mattncsu/ESPixelClock/examples/ESPixelClock/patterns.h

/*
   ESP32 FastLED WebServer: https://github.com/jasoncoon/esp32-fastled-webserver
   Copyright (C) 2017 Jason Coon

   Built upon the amazing FastLED work of Daniel Garcia and Mark Kriegsman:
   https://github.com/FastLED/FastLED

   ESP32 support provided by the hard work of Sam Guyer:
   https://github.com/samguyer/FastLED

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
   You should have received a copy of the GNU General Public License
   along with this program.  If not, see <http://www.gnu.org/licenses/>.
*/

#include "palettes.h";
#include "twinkleFox.h"
#include "map.h"
#include "noise.h"

void rainbow()
{
  // FastLED's built-in rainbow generator
  fill_rainbow( leds, NUM_LEDS, gHue, speed);
}

void addGlitter( fract8 chanceOfGlitter)
{
  if ( random8() < chanceOfGlitter) {
    leds[ random16(NUM_LEDS) ] += CRGB::White;
  }
}

void rainbowWithGlitter()
{
  // built-in FastLED rainbow, plus some random sparkly glitter
  rainbow();
  addGlitter(80);
}

void confetti()
{
  // random colored speckles that blink in and fade smoothly
  fadeToBlackBy( leds, NUM_LEDS, 10);
  int pos = random16(NUM_LEDS);
  leds[pos] += CHSV( gHue + random8(64), 200, 255);
}

void sinelon()
{
  // a colored dot sweeping back and forth, with fading trails
  fadeToBlackBy( leds, NUM_LEDS, 20);
  int pos = beatsin16(speed, 0, NUM_LEDS - 1);
  static int prevpos = 0;
  CRGB color = ColorFromPalette(palettes[currentPaletteIndex], gHue, 255);
  if ( pos < prevpos ) {
    fill_solid( leds + pos, (prevpos - pos) + 1, color);
  } else {
    fill_solid( leds + prevpos, (pos - prevpos) + 1, color);
  }
  prevpos = pos;
}

void bpm()
{
  // colored stripes pulsing at a defined Beats-Per-Minute (BPM)
  uint8_t beat = beatsin8( speed, 64, 255);
  CRGBPalette16 palette = palettes[currentPaletteIndex];
  for ( int i = 0; i < NUM_LEDS; i++) {
    leds[i] = ColorFromPalette(palette, gHue + (i * 2), beat - gHue + (i * 10));
  }
}

void juggle() {
  // eight colored dots, weaving in and out of sync with each other
  fadeToBlackBy( leds, NUM_LEDS, 20);
  byte dothue = 0;
  for ( int i = 0; i < 8; i++) {
    leds[beatsin16( i + speed, 0, NUM_LEDS - 1 )] |= CHSV(dothue, 200, 255);
    dothue += 32;
  }
}

void showSolidColor()
{
  fill_solid(leds, NUM_LEDS, solidColor);
}

// based on FastLED example Fire2012WithPalette: https://github.com/FastLED/FastLED/blob/master/examples/Fire2012WithPalette/Fire2012WithPalette.ino
void heatMap(CRGBPalette16 palette, bool up)
{
  fill_solid(leds, NUM_LEDS, CRGB::Black);

  // Add entropy to random number generator; we use a lot of it.
  random16_add_entropy(random(256));

  // Array of temperature readings at each simulation cell
  static byte heat[NUM_LEDS];

  byte colorindex;

  // Step 1.  Cool down every cell a little
  for ( uint16_t i = 0; i < NUM_LEDS; i++) {
    heat[i] = qsub8( heat[i],  random8(0, ((cooling * 10) / NUM_LEDS) + 2));
  }

  // Step 2.  Heat from each cell drifts 'up' and diffuses a little
  for ( uint16_t k = NUM_LEDS - 1; k >= 2; k--) {
    heat[k] = (heat[k - 1] + heat[k - 2] + heat[k - 2] ) / 3;
  }

  // Step 3.  Randomly ignite new 'sparks' of heat near the bottom
  if ( random8() < sparking ) {
    int y = random8(7);
    heat[y] = qadd8( heat[y], random8(160, 255) );
  }

  // Step 4.  Map from heat cells to LED colors
  for ( uint16_t j = 0; j < NUM_LEDS; j++) {
    // Scale the heat value from 0-255 down to 0-240
    // for best results with color palettes.
    colorindex = scale8(heat[j], 190);

    CRGB color = ColorFromPalette(palette, colorindex);

    if (up) {
      leds[j] = color;
    }
    else {
      leds[(NUM_LEDS - 1) - j] = color;
    }
  }
}

void fire()
{
  heatMap(HeatColors_p, true);
}

void water()
{
  heatMap(IceColors_p, false);
}

// Pride2015 by Mark Kriegsman: https://gist.github.com/kriegsman/964de772d64c502760e5
// This function draws rainbows with an ever-changing,
// widely-varying set of parameters.
void pride()
{
  static uint16_t sPseudotime = 0;
  static uint16_t sLastMillis = 0;
  static uint16_t sHue16 = 0;

  uint8_t sat8 = beatsin88( 87, 220, 250);
  uint8_t brightdepth = beatsin88( 341, 96, 224);
  uint16_t brightnessthetainc16 = beatsin88( 203, (25 * 256), (40 * 256));
  uint8_t msmultiplier = beatsin88(147, 23, 60);

  uint16_t hue16 = sHue16;//gHue * 256;
  uint16_t hueinc16 = beatsin88(113, 1, 3000);

  uint16_t ms = millis();
  uint16_t deltams = ms - sLastMillis ;
  sLastMillis  = ms;
  sPseudotime += deltams * msmultiplier;
  sHue16 += deltams * beatsin88( 400, 5, 9);
  uint16_t brightnesstheta16 = sPseudotime;

  for ( uint16_t i = 0 ; i < NUM_LEDS; i++) {
    hue16 += hueinc16;
    uint8_t hue8 = hue16 / 256;

    brightnesstheta16  += brightnessthetainc16;
    uint16_t b16 = sin16( brightnesstheta16  ) + 32768;

    uint16_t bri16 = (uint32_t)((uint32_t)b16 * (uint32_t)b16) / 65536;
    uint8_t bri8 = (uint32_t)(((uint32_t)bri16) * brightdepth) / 65536;
    bri8 += (255 - brightdepth);

    CRGB newcolor = CHSV( hue8, sat8, bri8);

    uint16_t pixelnumber = i;
    pixelnumber = (NUM_LEDS - 1) - pixelnumber;

    nblend( leds[pixelnumber], newcolor, 64);
  }
}

// ColorWavesWithPalettes by Mark Kriegsman: https://gist.github.com/kriegsman/8281905786e8b2632aeb
// This function draws color waves with an ever-changing,
// widely-varying set of parameters, using a color palette.
void colorwaves( CRGB* ledarray, uint16_t numleds, CRGBPalette16& palette)
{
  static uint16_t sPseudotime = 0;
  static uint16_t sLastMillis = 0;
  static uint16_t sHue16 = 0;

  // uint8_t sat8 = beatsin88( 87, 220, 250);
  uint8_t brightdepth = beatsin88( 341, 96, 224);
  uint16_t brightnessthetainc16 = beatsin88( 203, (25 * 256), (40 * 256));
  uint8_t msmultiplier = beatsin88(147, 23, 60);

  uint16_t hue16 = sHue16;//gHue * 256;
  uint16_t hueinc16 = beatsin88(113, 300, 1500);

  uint16_t ms = millis();
  uint16_t deltams = ms - sLastMillis ;
  sLastMillis  = ms;
  sPseudotime += deltams * msmultiplier;
  sHue16 += deltams * beatsin88( 400, 5, 9);
  uint16_t brightnesstheta16 = sPseudotime;

  for ( uint16_t i = 0 ; i < numleds; i++) {
    hue16 += hueinc16;
    uint8_t hue8 = hue16 / 256;
    uint16_t h16_128 = hue16 >> 7;
    if ( h16_128 & 0x100) {
      hue8 = 255 - (h16_128 >> 1);
    } else {
      hue8 = h16_128 >> 1;
    }

    brightnesstheta16  += brightnessthetainc16;
    uint16_t b16 = sin16( brightnesstheta16  ) + 32768;

    uint16_t bri16 = (uint32_t)((uint32_t)b16 * (uint32_t)b16) / 65536;
    uint8_t bri8 = (uint32_t)(((uint32_t)bri16) * brightdepth) / 65536;
    bri8 += (255 - brightdepth);

    uint8_t index = hue8;
    //index = triwave8( index);
    index = scale8( index, 240);

    CRGB newcolor = ColorFromPalette( palette, index, bri8);

    uint16_t pixelnumber = i;
    pixelnumber = (numleds - 1) - pixelnumber;

    nblend( ledarray[pixelnumber], newcolor, 128);
  }
}

void colorWaves()
{
  colorwaves(leds, NUM_LEDS, currentPalette);
}

void strandTest()
{
  uint8_t i = speed;

  if (speed >= NUM_LEDS) speed = NUM_LEDS - 1;

  fill_solid(leds, NUM_LEDS, CRGB::Black);

  leds[i] = solidColor;
}

typedef void (*Pattern)();
typedef Pattern PatternList[];
typedef struct {
  Pattern pattern;
  String name;
} PatternAndName;
typedef PatternAndName PatternAndNameList[];

PatternAndNameList patterns = {
  { pride,                  "Pride" },
  { colorWaves,             "Color Waves" },

  // matrix patterns
  { xyTest,    "XY Test" },
  { xPalette,  "X Axis Palette" },
  { yPalette,  "Y Axis Palette" },
  { xyPalette, "XY Axis Palette" },
  { xGradientPalette,  "X Axis Gradient Palette" },
  { yGradientPalette,  "Y Axis Gradient Palette" },
  { xyGradientPalette, "XY Axis Gradient Palette" },

  // noise patterns
  { fireNoise, "Fire Noise" },
  { fireNoise2, "Fire Noise 2" },
  { lavaNoise, "Lava Noise" },
  { rainbowNoise, "Rainbow Noise" },
  { rainbowStripeNoise, "Rainbow Stripe Noise" },
  { partyNoise, "Party Noise" },
  { forestNoise, "Forest Noise" },
  { cloudNoise, "Cloud Noise" },
  { oceanNoise, "Ocean Noise" },
  { blackAndWhiteNoise, "Black & White Noise" },
  { blackAndBlueNoise, "Black & Blue Noise" },

  // TwinkleFOX patterns
  { drawTwinkles, "Twinkles" },

  // Fire & Water
  { fire, "Fire" },
  { water, "Water" },

  // DemoReel100 patterns
  { rainbow, "rainbow" },
  { rainbowWithGlitter, "rainbowWithGlitter" },
  { confetti, "confetti" },
  { sinelon, "sinelon" },
  { juggle, "juggle" },
  { bpm, "bpm" },

  { strandTest,             "Strand Test" },

  { showSolidColor,         "Solid Color" },
};

const uint8_t patternCount = ARRAY_SIZE(patterns);
