mattncsu/ESPixelClock/examples/ESPixelClock/field.h

/*
   ESP32 FastLED WebServer: https://github.com/jasoncoon/esp32-fastled-webserver
   Copyright (C) 2017 Jason Coon

   Built upon the amazing FastLED work of Daniel Garcia and Mark Kriegsman:
   https://github.com/FastLED/FastLED

   ESP32 support provided by the hard work of Sam Guyer:
   https://github.com/samguyer/FastLED

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
   You should have received a copy of the GNU General Public License
   along with this program.  If not, see <http://www.gnu.org/licenses/>.
*/

typedef String (*FieldSetter)(String);
typedef String (*FieldGetter)();

const String NumberFieldType = "Number";
const String BooleanFieldType = "Boolean";
const String SelectFieldType = "Select";
const String ColorFieldType = "Color";
const String SectionFieldType = "Section";

typedef struct Field {
  public:
    String name;
    String label;
    String type;
    int min;
    int max;
    FieldGetter getValue;
    FieldGetter getOptions;
    FieldSetter setValue;
};

typedef Field FieldList[];

Field getField(String name, FieldList fields, uint8_t count) {
  for (uint8_t i = 0; i < count; i++) {
    Field field = fields[i];
    if (field.name == name) {
      return field;
    }
  }
  return Field();
}

String getFieldValue(String name, FieldList fields, uint8_t count) {
  Field field = getField(name, fields, count);
  if (field.getValue) {
    return field.getValue();
  }
  return String();
}

CRGB parseColor(String value) {  
  uint8_t ri = value.indexOf(",");
  uint8_t gi = value.indexOf(",", ri + 1);

  String rs = value.substring(0, ri);
  String gs = value.substring(ri + 1, gi);
  String bs = value.substring(gi + 1);

  uint8_t r = rs.toInt();
  uint8_t g = gs.toInt();
  uint8_t b = bs.toInt();

  return CRGB(r, g, b);
}

void writeFieldsToEEPROM(FieldList fields, uint8_t count) {
  uint8_t index = 0;

  EEPROM.write(index, 0);

  for (uint8_t i = 0; i < count; i++) {
    Field field = fields[i];
    if (!field.getValue && !field.setValue)
      continue;

    String value = field.getValue();

    if (field.type == ColorFieldType) {
      CRGB color = parseColor(value);
      EEPROM.write(index++, color.r);
      EEPROM.write(index++, color.g);
      EEPROM.write(index++, color.b);
    } else if (field.name == "timezoneOffset") {
      int i = value.toInt();
      byte v = i - field.min;
      EEPROM.write(index++, v);
    } else {
      byte v = value.toInt();
      EEPROM.write(index++, v);
    }
  
    Serial.print("Wrote field: "); Serial.print(i);
    Serial.print(", name: "); Serial.print(field.name);
    Serial.print(", value: "); Serial.println(field.getValue());
  }

  EEPROM.commit();
}

//String setFieldValue(String name, String value, FieldList fields, uint8_t count) {
//  String result;
//
//  Field field = getField(name, fields, count);
//  if (field.setValue) {
//    if (field.type == ColorFieldType) {
//      String r = webServer.arg("r");
//      String g = webServer.arg("g");
//      String b = webServer.arg("b");
//      String combinedValue = r + "," + g + "," + b;
//      result = field.setValue(combinedValue);
//    } else {
//      result = field.setValue(value);
//    }
//  }
//
//  writeFieldsToEEPROM(fields, count);
//
//  return result;
//}

String setFieldValueAsync(String name, String value, FieldList fields, uint8_t count) {
  String result;

  Field field = getField(name, fields, count);
  if (field.setValue) {
      result = field.setValue(value);
    
  }

  writeFieldsToEEPROM(fields, count);

  return result;
}


void loadFieldsFromEEPROM(FieldList fields, uint8_t count) {
  uint8_t byteCount = 1;

  for (uint8_t i = 0; i < count; i++) {
    Field field = fields[i];
    if (!field.setValue)
      continue;

    if (field.type == ColorFieldType) {
      byteCount += 3;
    } else {
      byteCount++;
    }
  }

  if (!EEPROM.begin(count)) {
    Serial.println("Failed to initialize EEPROM!");
    return;
  }

  if (EEPROM.read(0) == 255) {
    Serial.println("First run, or EEPROM erased, skipping settings load!");
    return;
  }

  uint8_t index = 0;

  for (uint8_t i = 0; i < count; i++) {
    Field field = fields[i];
    if (!field.setValue)
      continue;

    if (field.type == ColorFieldType) {
      String r = String(EEPROM.read(index++));
      String g = String(EEPROM.read(index++));
      String b = String(EEPROM.read(index++));
      field.setValue(r + "," + g + "," + b);
    } else if (field.name == "timezoneOffset") {
      byte b = EEPROM.read(index++);
      int v = b + field.min;
      field.setValue(String(v));
    } else {
      byte v = EEPROM.read(index++);
      field.setValue(String(v));
    }
  
    Serial.print("Loaded field: "); Serial.print(i);
    Serial.print(", name: "); Serial.print(field.name);
    Serial.print(", value: "); Serial.println(field.getValue());
  }
}

String getFieldsJson(FieldList fields, uint8_t count) {
  String json = "[";

  for (uint8_t i = 0; i < count; i++) {
    Field field = fields[i];

    json += "{\"name\":\"" + field.name + "\",\"label\":\"" + field.label + "\",\"type\":\"" + field.type + "\"";

    if (field.getValue) {
      if (field.type == ColorFieldType || field.type == "String") {
        json += ",\"value\":\"" + field.getValue() + "\"";
      }
      else {
        json += ",\"value\":" + field.getValue();
      }
    }

    if (field.type == NumberFieldType) {
      json += ",\"min\":" + String(field.min);
      json += ",\"max\":" + String(field.max);
    }

    if (field.getOptions) {
      json += ",\"options\":[";
      json += field.getOptions();
      json += "]";
    }

    json += "}";

    if (i < count - 1)
      json += ",";
  }

  json += "]";

  return json;
}
